fl4p/buck-tpsm33610/docs/2026-09-13-floorplan-compact-airwires.webp

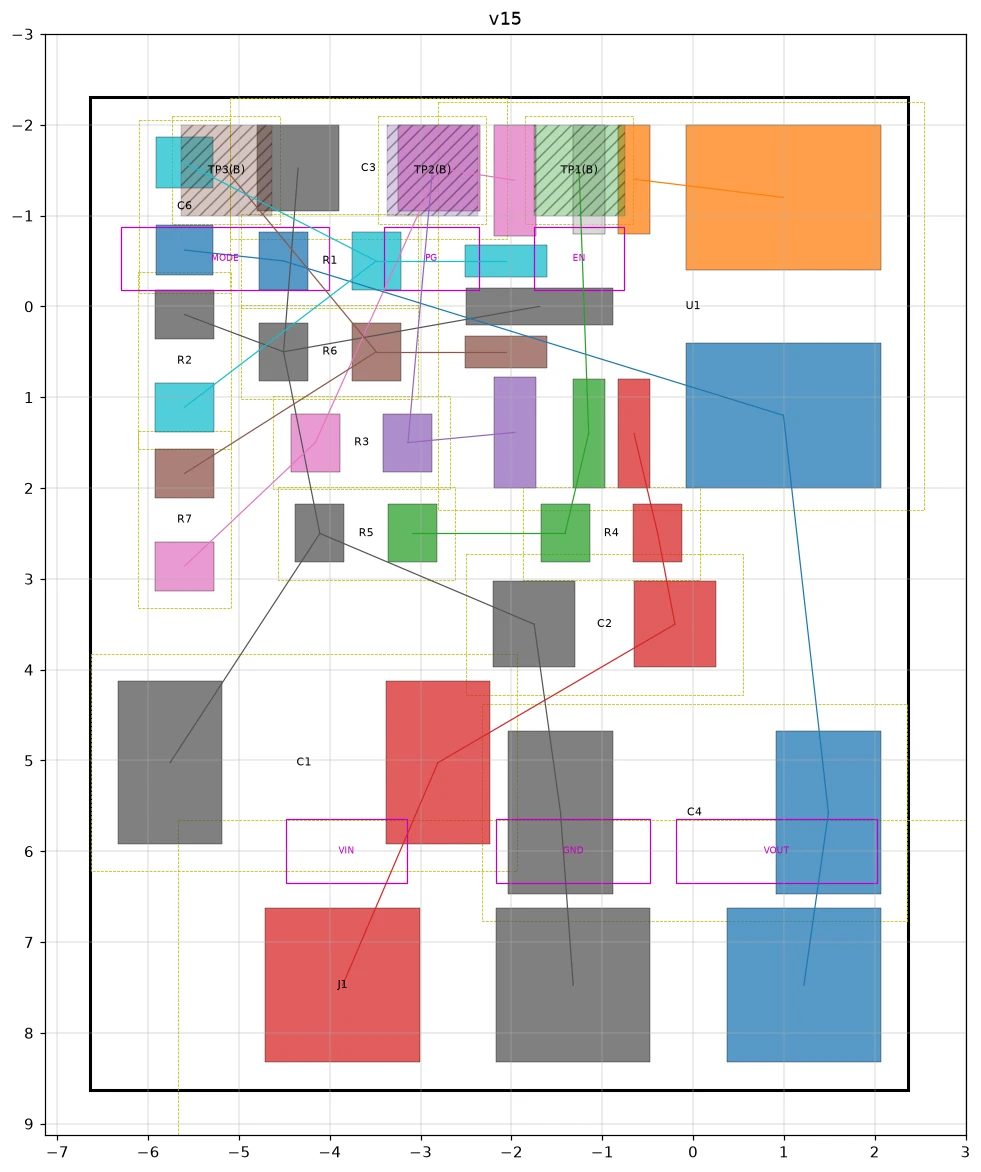
docs/2026-09-13-floorplan-compact-airwires.webp
