fl4p/buck-tpsm33610/docs/2026-09-13-floorplan-compact-top.webp

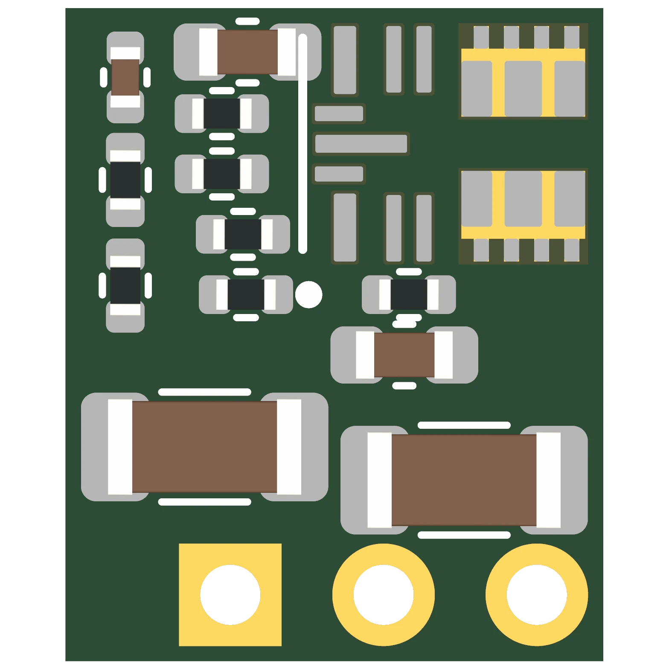
docs/2026-09-13-floorplan-compact-top.webp
